AlejoPm03/MSC23/design/analog_voltage_sensor.asc

C1: cap; 100n
C2: cap; 100n
C3: cap; 100n
R1: res; 100k
R2: res; 100k
R3: res; 100k
R4: res; 100k
R5: res; 10k
R7: res; 10k
R8: res; 5k6
R9: res; 5k6
R10: res; 5k6
R11: res; 2k2
R12: res; 2k2
U1: LM324_NS
U2: LM324_NS
V1: voltage; 15
V2: voltage; SINE(); AC 12
V3: voltage; PULSE(0 16 0 500m 500m 0 1)
V4: voltage; PULSE(0 16 0 500m 500m 0 1)
Named nets: 0, Vcc, Vin+, Vin-, Vopamp-, Vopamp+
.ac dec 1Meg 1 1Meg
