AlejoPm03/MSC23/firmware/Core/Inc/utils.h

#ifndef UTILS_H
#define UTILS_H
#include <stdio.h>
#include "main.h"

/**
 * Debugging macros
 */

#define LOG_INFO(x)       \
    {                     \
        printf("INFO: "); \
        printf(x);        \
        printf("\n");      \
    }
#define LOG_WARN(x)       \
    {                     \
        printf("WARN: "); \
        printf(x);        \
        printf("\n");      \
    }
#define LOG_ERROR(x)       \
    {                      \
        printf("ERROR: "); \
        printf(x);         \
        printf("\n");       \
    }


#endif
